ManiacalLabs/USBSwitchBuddy/img/2.jpg

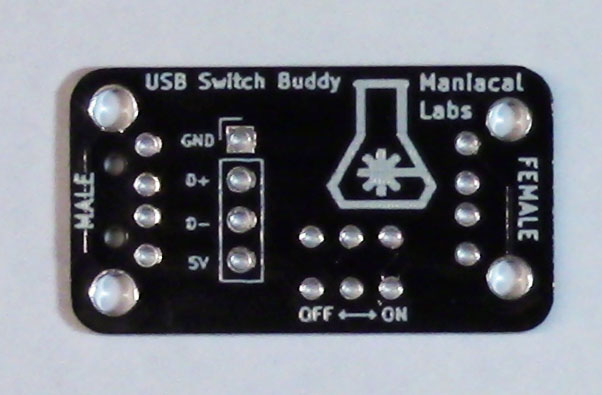
img/2.jpg
