ManiacalLabs/USBSwitchBuddy/img/4.jpg

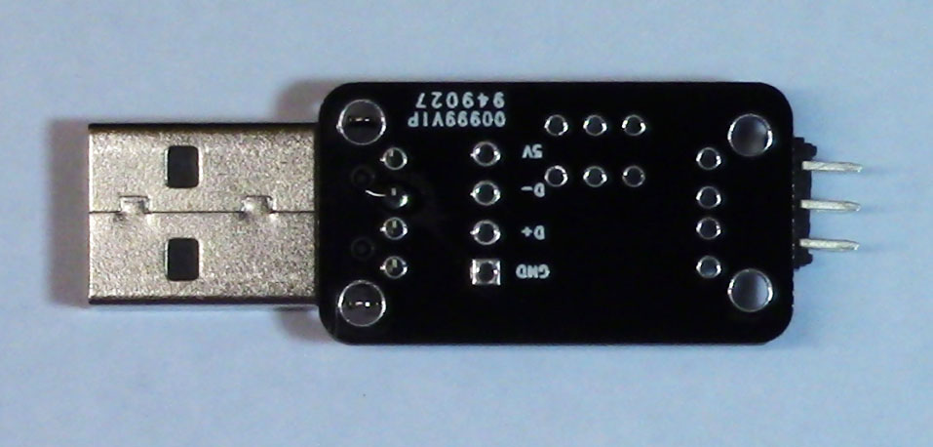
img/4.jpg
