ManiacalLabs/USBSwitchBuddy/img/5.jpg

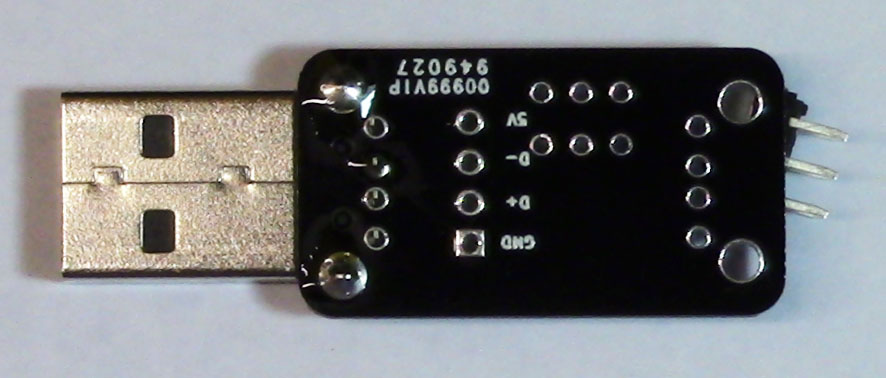
img/5.jpg
