ManiacalLabs/USBSwitchBuddy/img/6.jpg

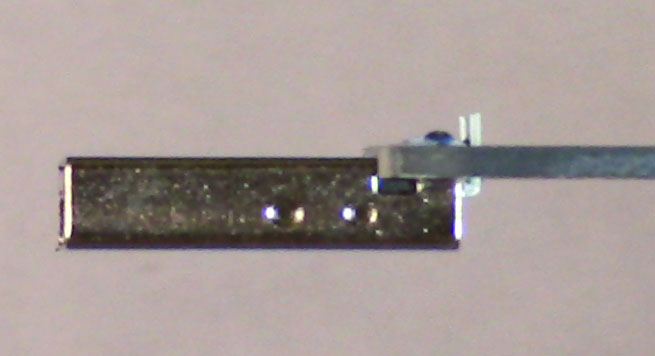
img/6.jpg
