ManiacalLabs/USBSwitchBuddy/img/10.jpg

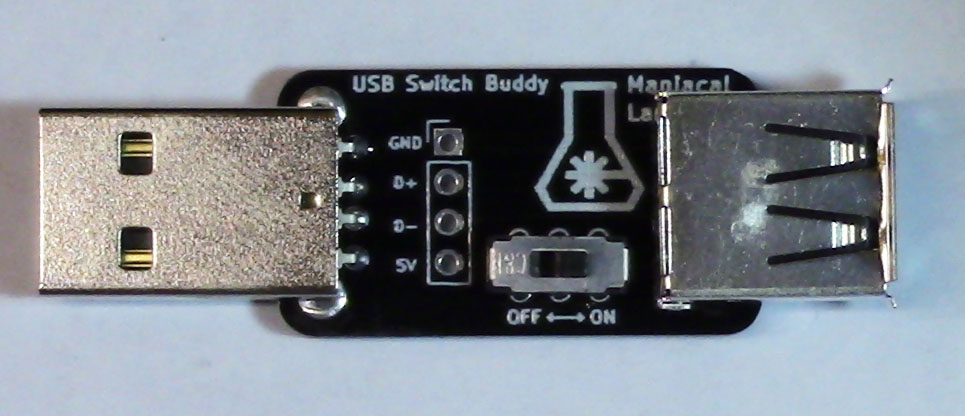
img/10.jpg
