ManiacalLabs/USBSwitchBuddy/img/11.jpg

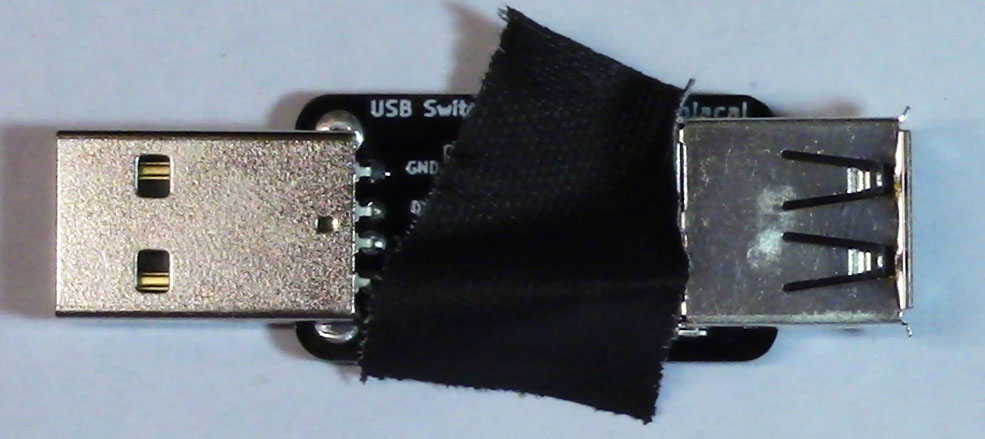
img/11.jpg
